andimoto/theme-yoyo/pics/004.JPG

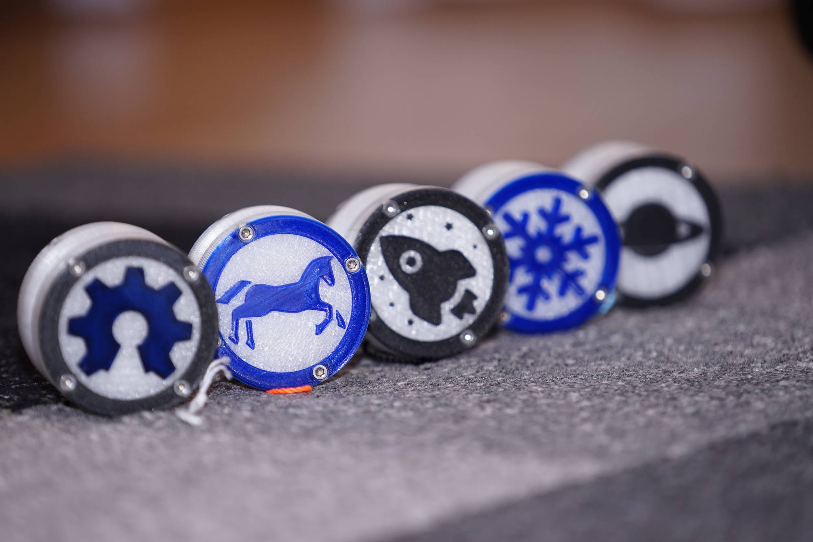
pics/004.JPG
