andimoto/theme-yoyo/pics/005.JPG

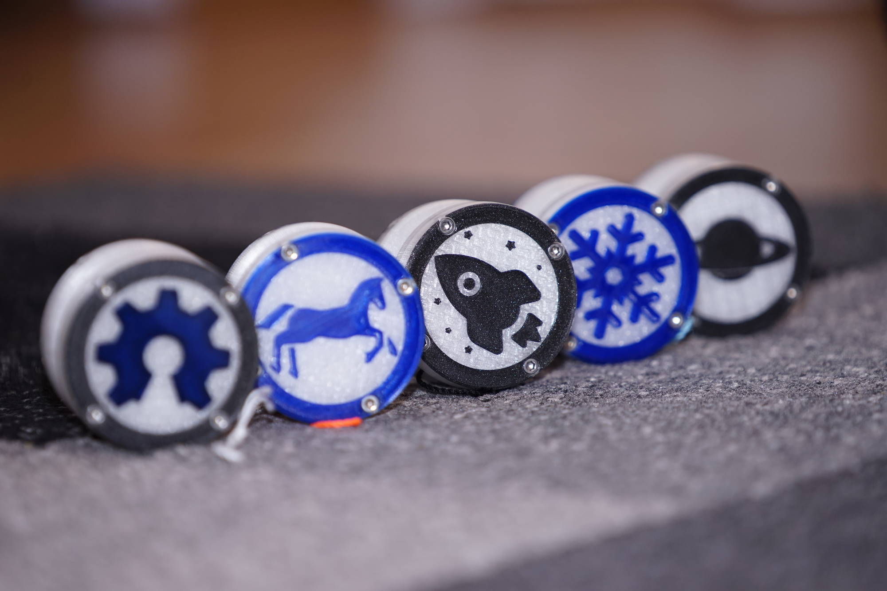
pics/005.JPG
