andimoto/theme-yoyo/svg/dinopixel.png

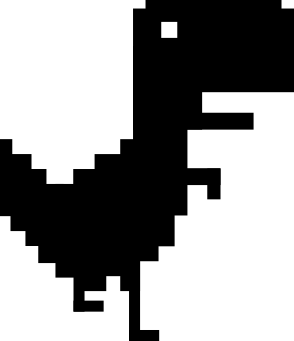
svg/dinopixel.png
